ampnics/GEN-AI-Based-timer-board-PCB/MHDK_03/images/image.png

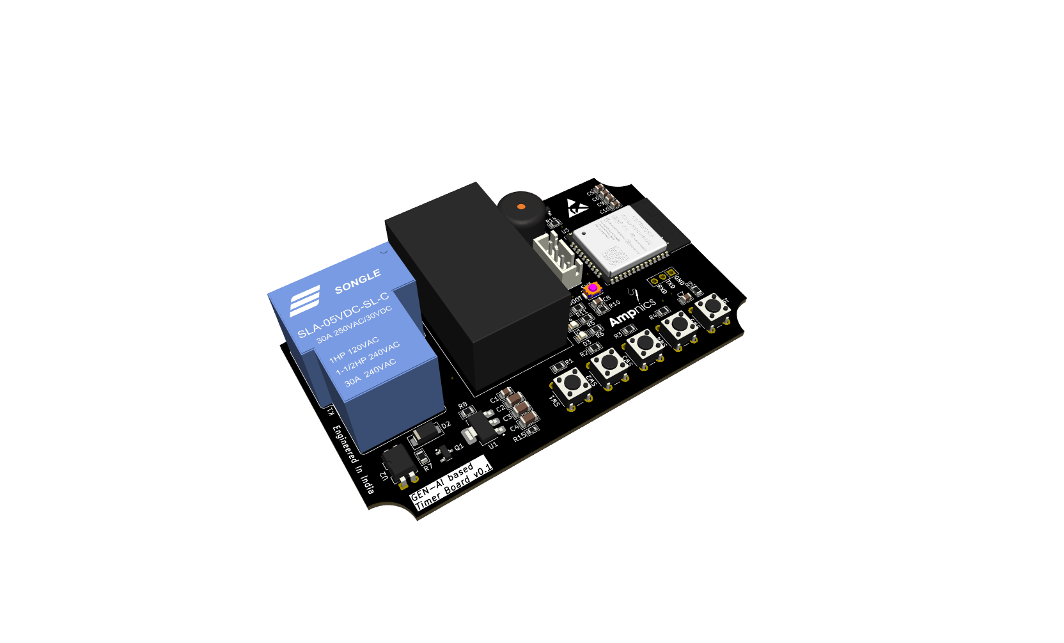
MHDK_03/images/image.png
